Flocloud9/GCC-3v-Cellphone-Rumble/images/v8/4bot.JPEG

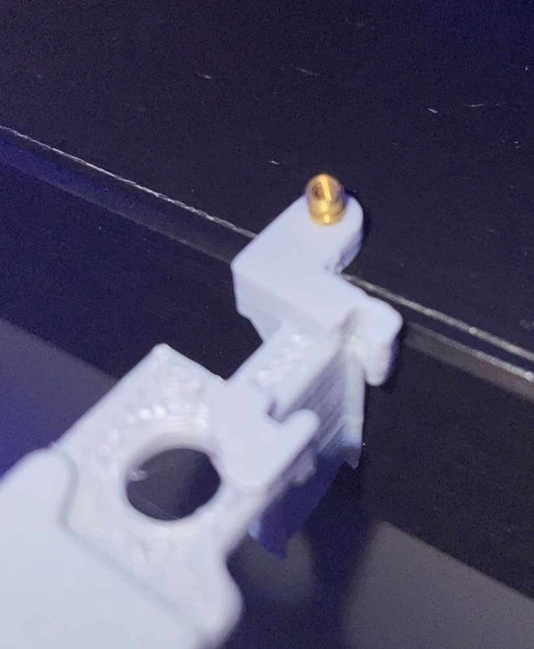
images/v8/4bot.JPEG
