Flocloud9/GCC-3v-Cellphone-Rumble/images/v8/9.JPEG

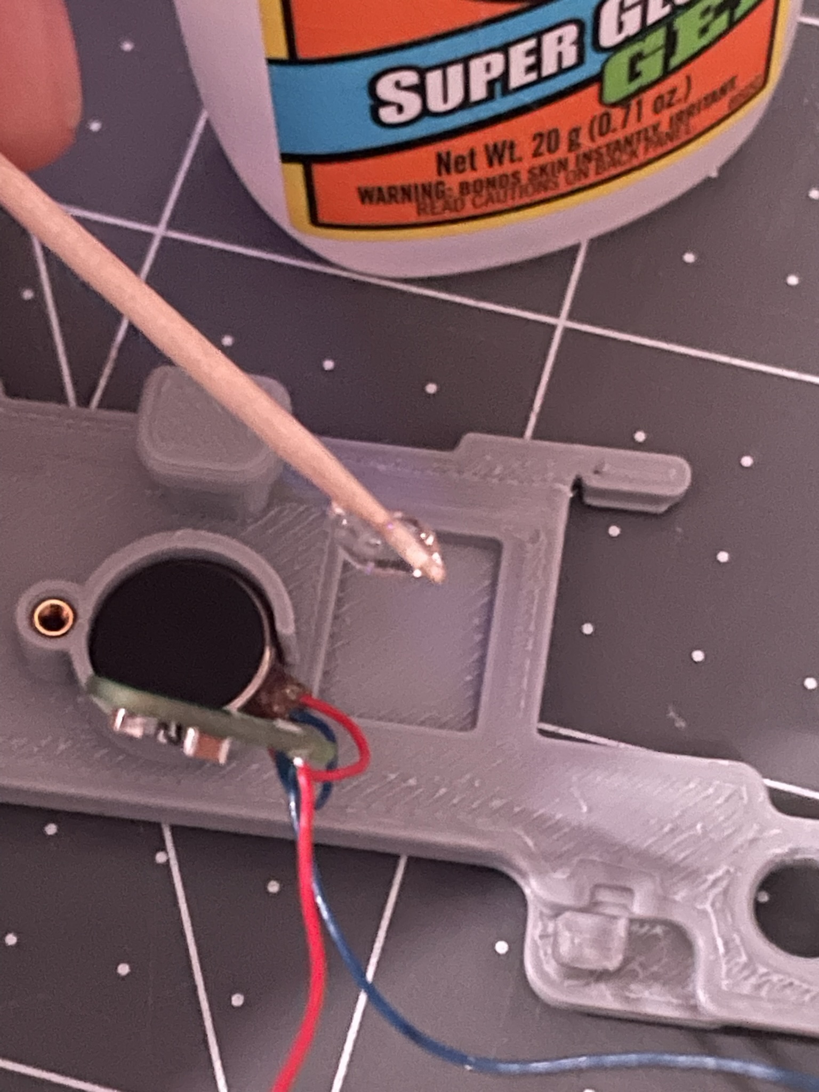
images/v8/9.JPEG
