Flocloud9/GCC-3v-Cellphone-Rumble/images/v8/flu.JPEG

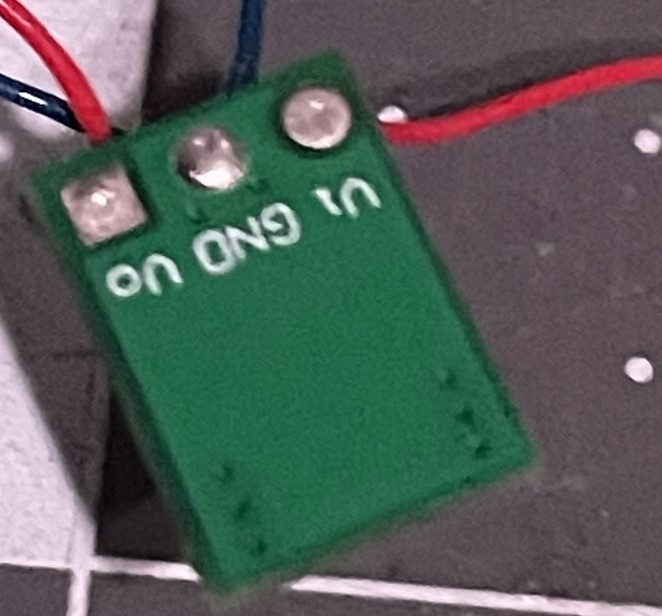
images/v8/flu.JPEG
