Flocloud9/GCC-3v-Cellphone-Rumble/images/v8/IMG_20230304_182826.jpg

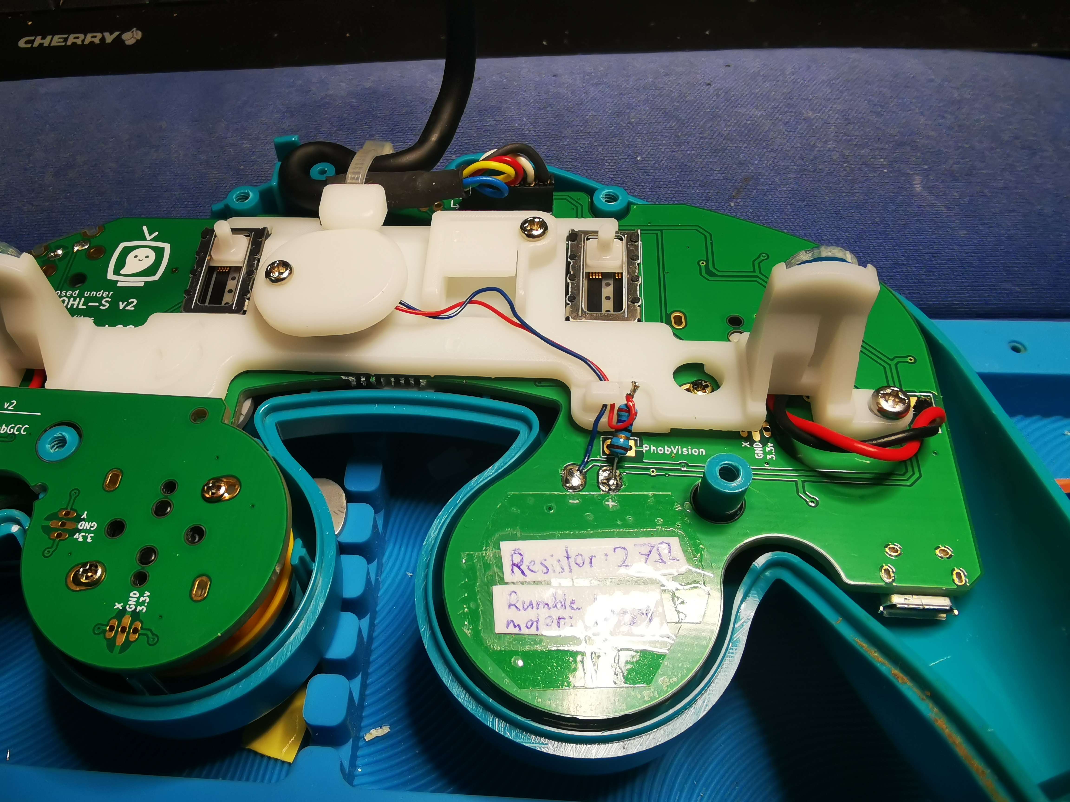
images/v8/IMG_20230304_182826.jpg
