Flocloud9/GCC-3v-Cellphone-Rumble/images/v8/pin1.JPEG

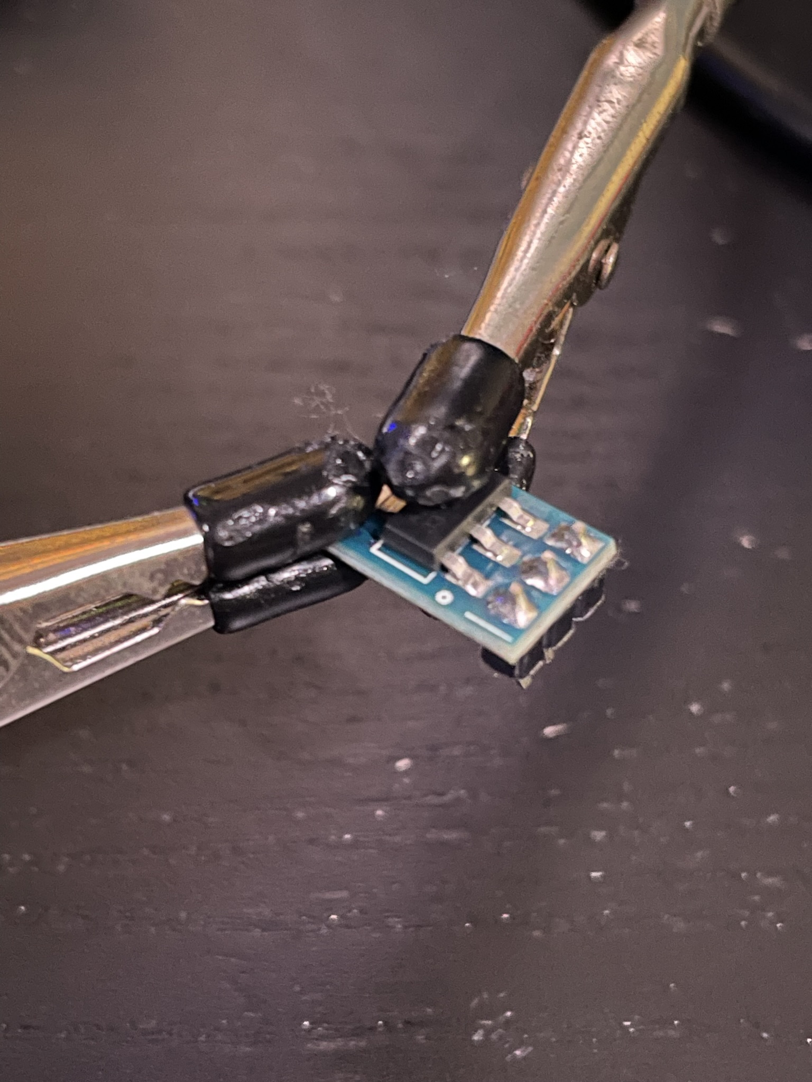
images/v8/pin1.JPEG
