Flocloud9/GCC-3v-Cellphone-Rumble/images/v8/pin2.JPEG

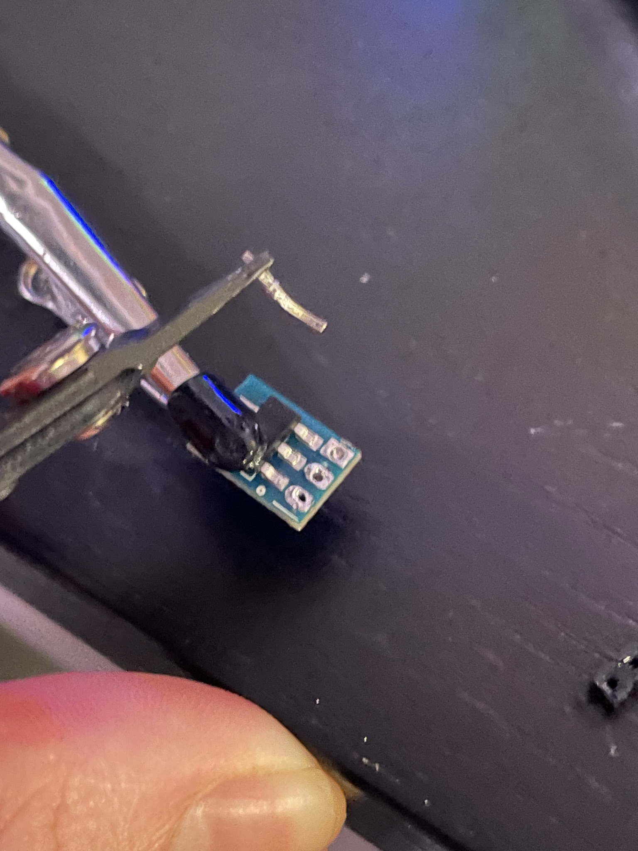
images/v8/pin2.JPEG
